Borzyszkowski/AutoRCCar/Multimedia and Sources/Management Picture.jpg

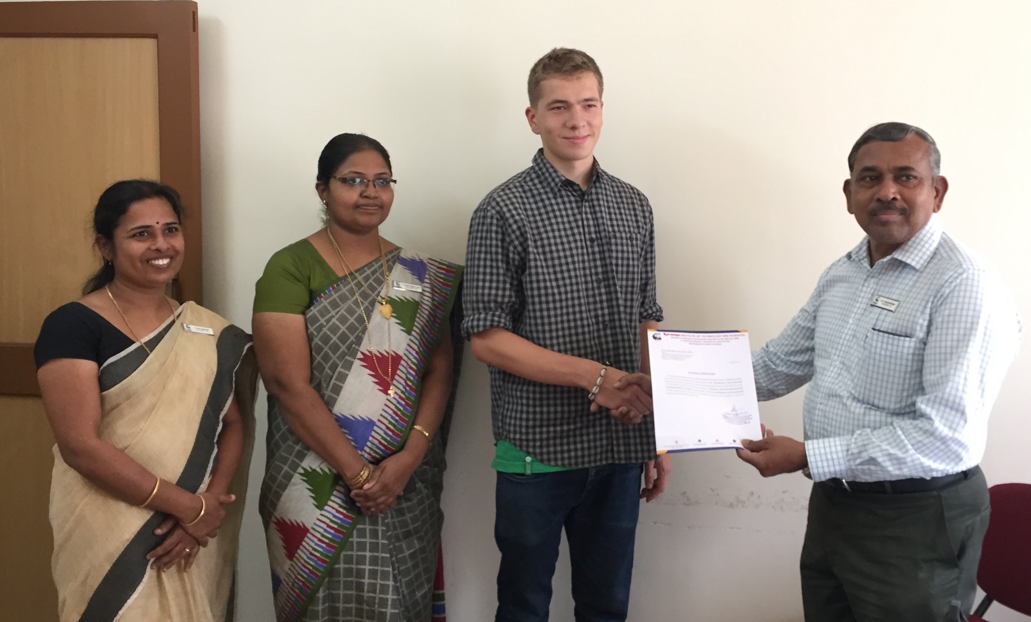
Multimedia and Sources/Management Picture.jpg
