Borzyszkowski/AutoRCCar/Multimedia and Sources/Mr. Chinnadurai Picture.jpg

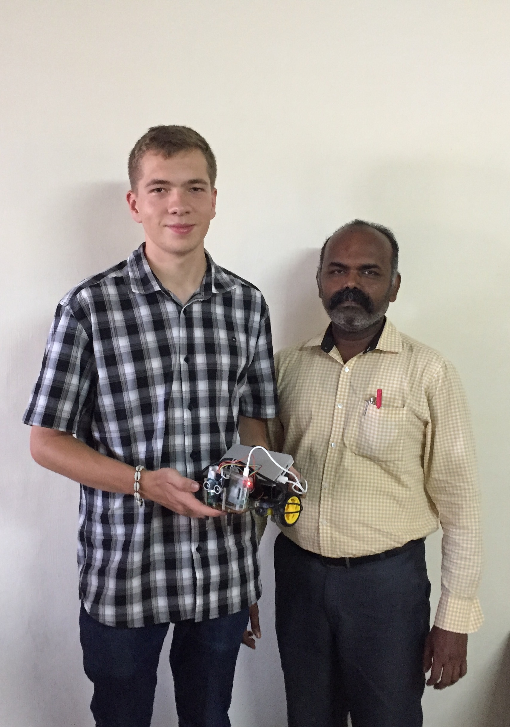
Multimedia and Sources/Mr. Chinnadurai Picture.jpg
