Borzyszkowski/AutoRCCar/Multimedia and Sources/Pictures/39468410_839187926285003_449385060995432448_n.jpg

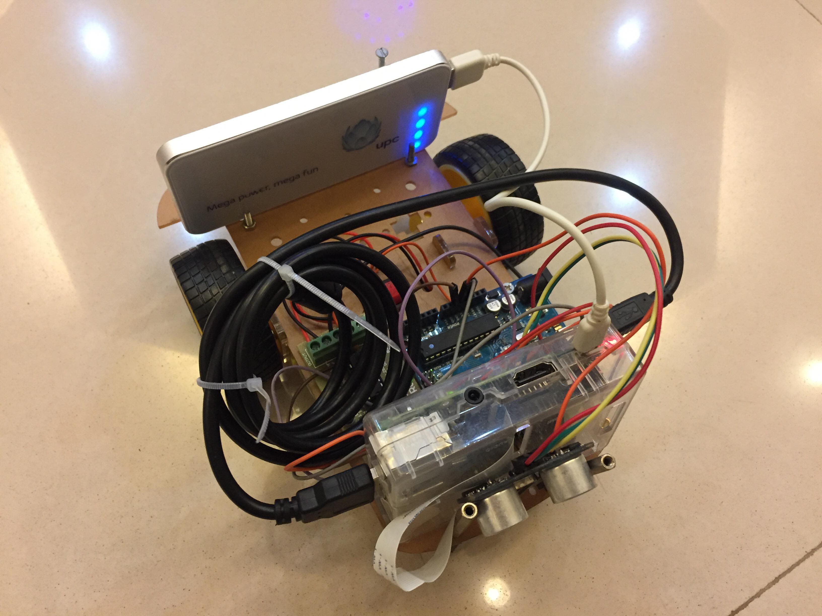
Multimedia and Sources/Pictures/39468410_839187926285003_449385060995432448_n.jpg
