Borzyszkowski/AutoRCCar/Multimedia and Sources/Pictures/39500178_2215699071837772_514372876871139328_n.jpg

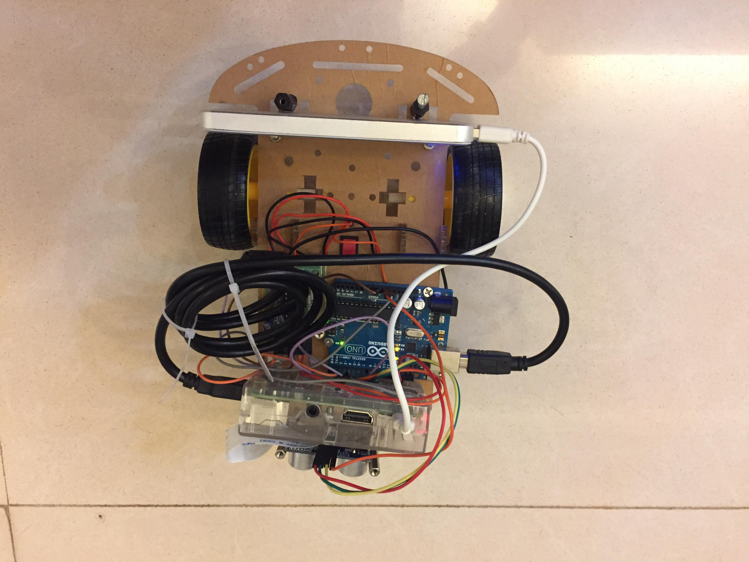
Multimedia and Sources/Pictures/39500178_2215699071837772_514372876871139328_n.jpg
