Borzyszkowski/AutoRCCar/Multimedia and Sources/Pictures/39558055_549934832104793_1728530642204884992_n.jpg

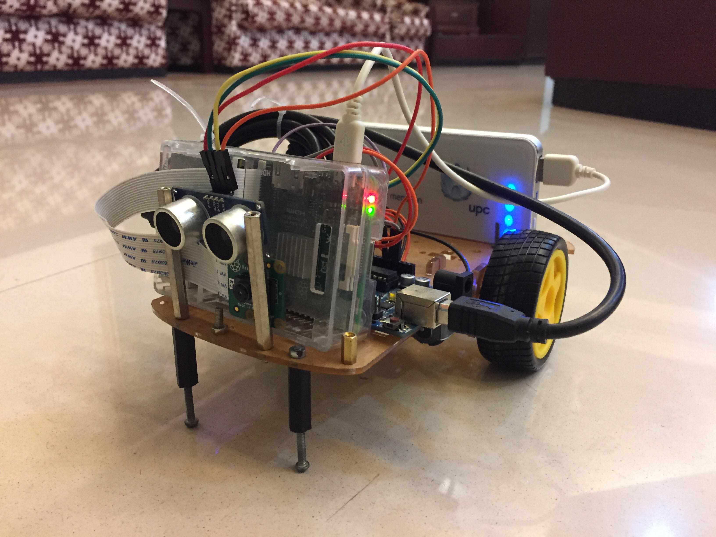
Multimedia and Sources/Pictures/39558055_549934832104793_1728530642204884992_n.jpg
