Borzyszkowski/AutoRCCar/Multimedia and Sources/Pictures/39700667_872723286234786_8544054784976486400_n.jpg

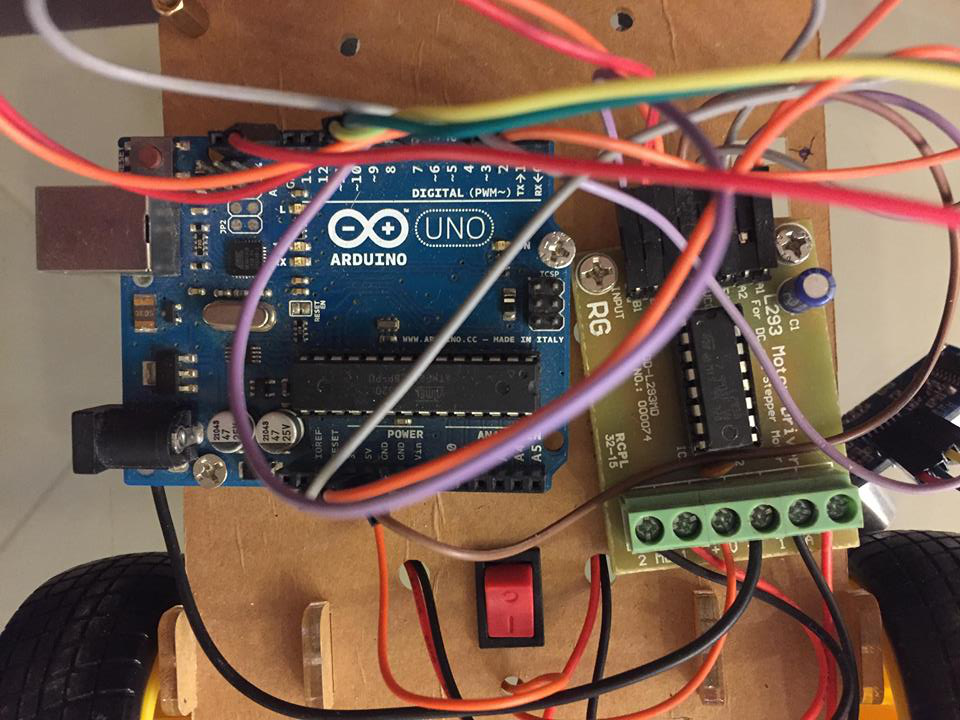
Multimedia and Sources/Pictures/39700667_872723286234786_8544054784976486400_n.jpg
