Borzyszkowski/AutoRCCar/Multimedia and Sources/Pictures/39714742_285751732237843_1191093236903444480_n.jpg

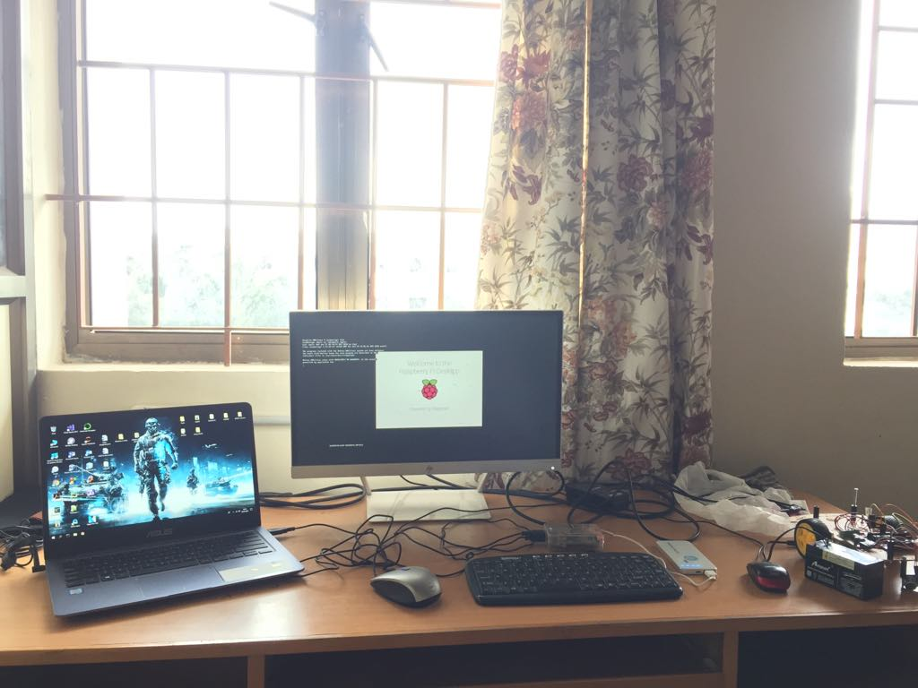
Multimedia and Sources/Pictures/39714742_285751732237843_1191093236903444480_n.jpg
