Borzyszkowski/AutoRCCar/Multimedia and Sources/Pictures/40152335_304728500334909_6182516082977275904_n.jpg

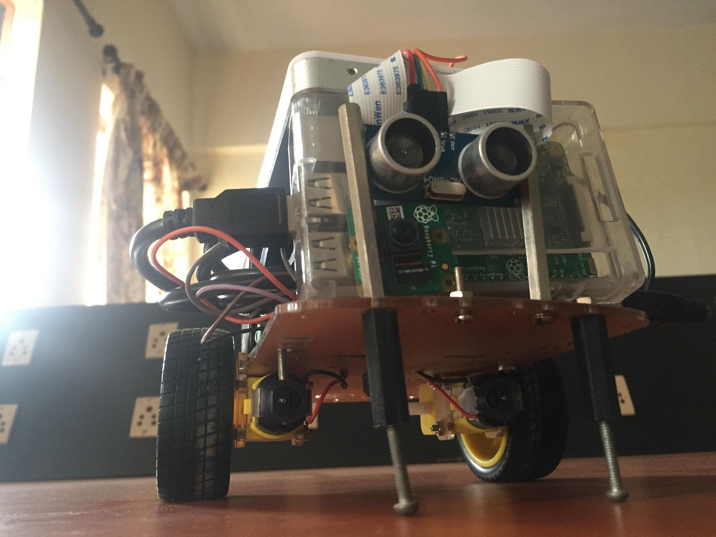
Multimedia and Sources/Pictures/40152335_304728500334909_6182516082977275904_n.jpg
