Borzyszkowski/AutoRCCar/Multimedia and Sources/Pictures/40215287_402138050315950_4970318549307359232_n.jpg

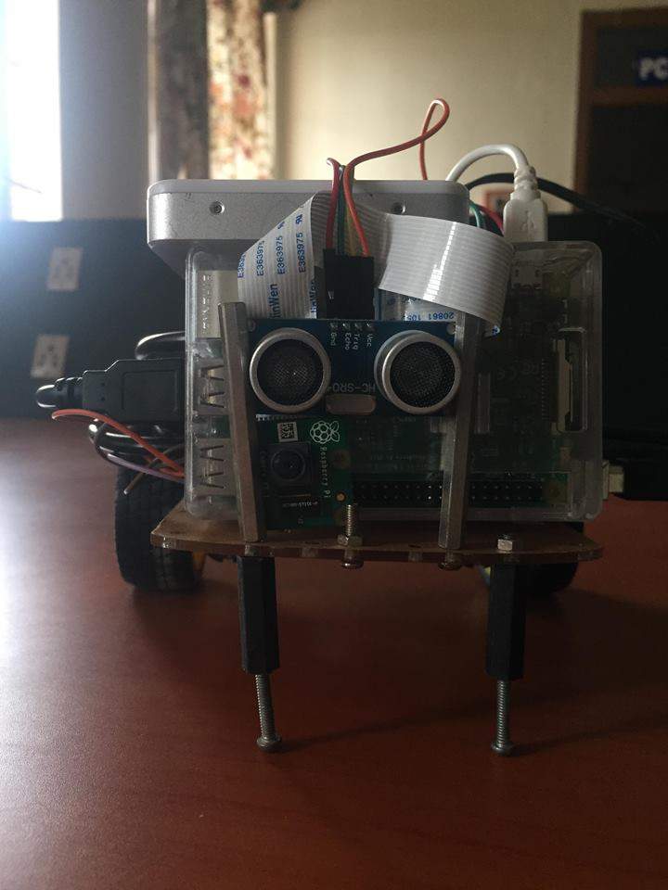
Multimedia and Sources/Pictures/40215287_402138050315950_4970318549307359232_n.jpg
