Borzyszkowski/AutoRCCar/Multimedia and Sources/Pictures/40229378_381721912364816_8785855984837853184_n.jpg

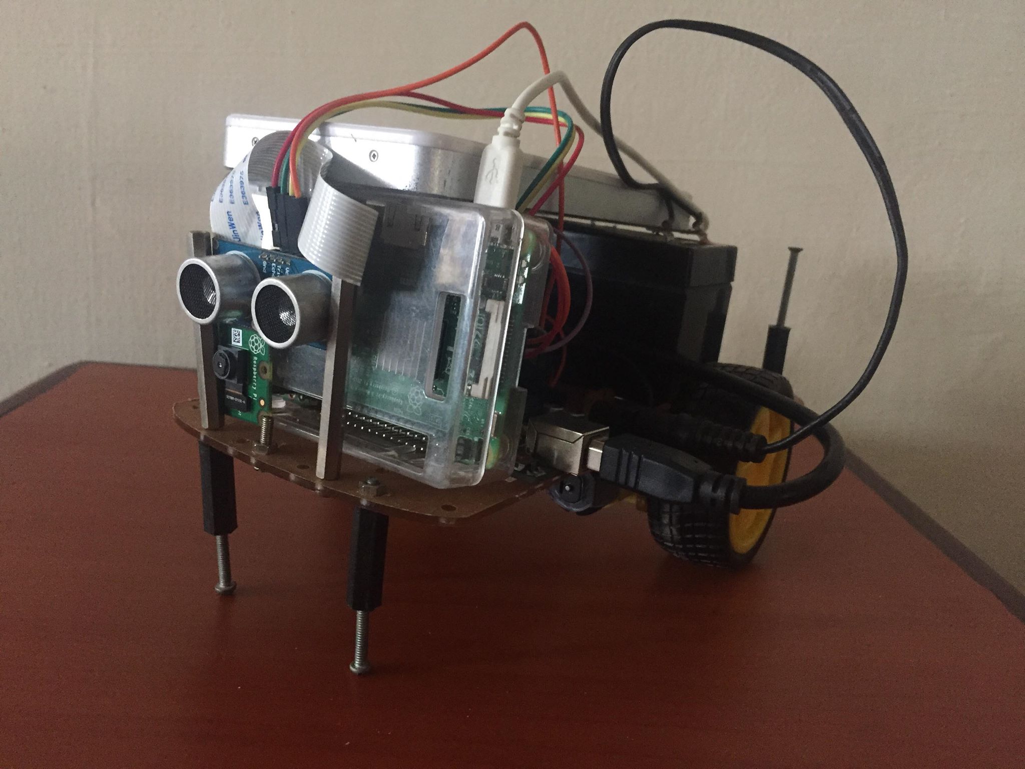
Multimedia and Sources/Pictures/40229378_381721912364816_8785855984837853184_n.jpg
