Borzyszkowski/AutoRCCar/Multimedia and Sources/Professor Rajasekaran Picture.jpg

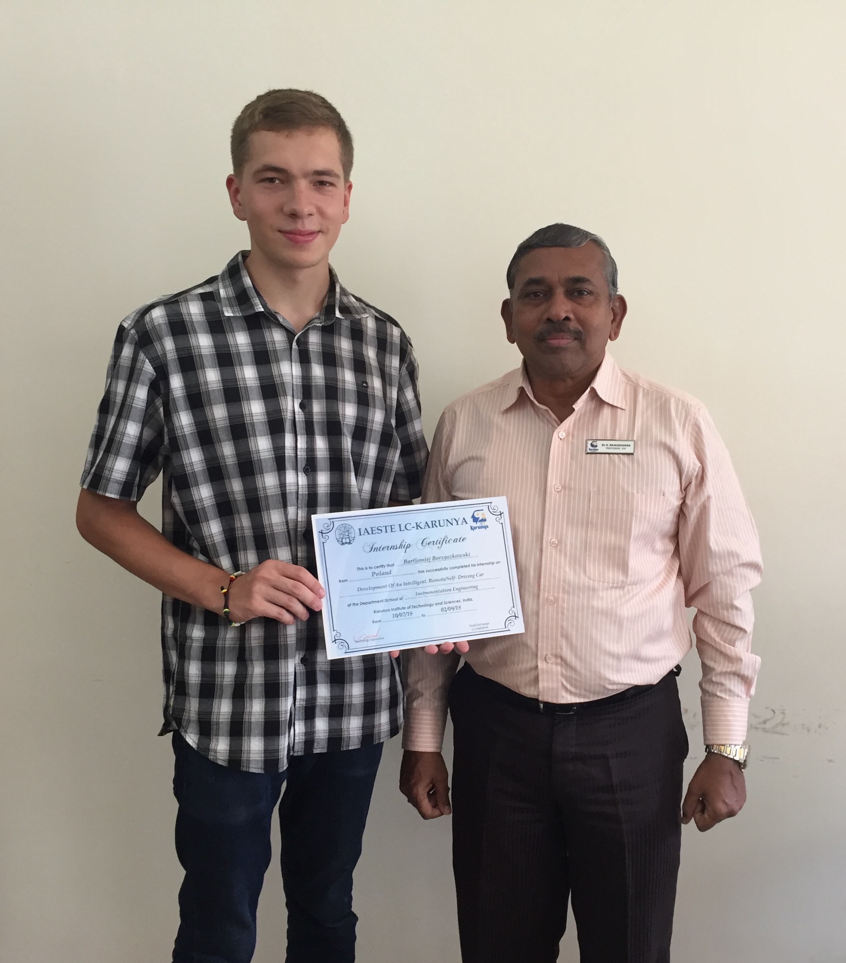
Multimedia and Sources/Professor Rajasekaran Picture.jpg
