Borzyszkowski/AutoRCCar/Multimedia and Sources/Scheme Arduino.png

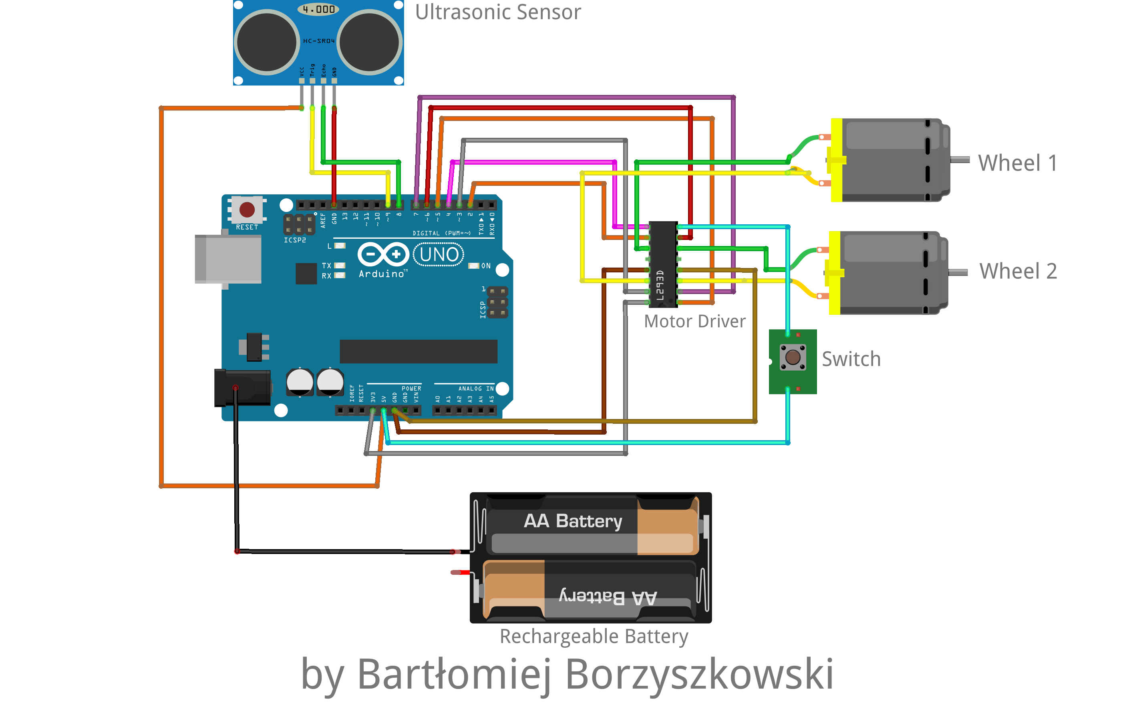
Multimedia and Sources/Scheme Arduino.png
